tlaasik/vgafb/src/VgaFB_modes.cpp

/*

VgaFB_modes.cpp

Minimalistic VGA framebuffer hardware and software for microcontrollers
https://github.com/tlaasik/vgafb/

-------------------------------------------------------------------------------

Copyright (c) 2017, toomas.laasik@gmail.com
All rights reserved.

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
-------------------------------------------------------------------------------

Timing info used is taken from here:
http://martin.hinner.info/vga/timing.html

*/
#include "VgaFB_core.h"

// VESA 800x600@60Hz  hsync:37.9kHz pxclk:40.0MHz  800 840 968 1056  600 601 605 628  +hsync +vsync
vgamode_t vgamode_400x300_60Hz_20MHz = { 400, 420, 484, 526,  600, 601, 605, 628,  2, VGAFLAG_NONE };
vgamode_t vgamode_240x240_60Hz_20MHz = { 240, 344, 408, 526,  480, 601, 605, 628,  2, VGAFLAG_NONE };

// VESA 640x480@75Hz  hsync:37.5kHz pxclk:31.5MHz  640 656 720 840  480 481 484 500  -hsync -vsync
// modified hTotal because 840/16=52.5. pxclk is not exact, this mode should ideally use 31.5MHz
vgamode_t vgamode_640x480_75Hz_32MHz = { 640, 656, 720, 848,  480, 481, 484, 500,  1, (vgaflags_t)(VGAFLAG_INVERTED_VSYNC | VGAFLAG_INVERTED_HSYNC) };
vgamode_t vgamode_320x240_75Hz_16MHz = { 320, 328, 360, 424,  480, 481, 484, 500,  2, (vgaflags_t)(VGAFLAG_INVERTED_VSYNC | VGAFLAG_INVERTED_HSYNC) };

// VESA 640x400@85Hz  hsync:37.9kHz pxclk:31.5MHz  640 672 736 832  400 401 404 445 -hsync +vsync
vgamode_t vgamode_640x400_85Hz_32MHz = { 640, 672, 736, 832,  400, 401, 404, 445,  1, VGAFLAG_INVERTED_HSYNC };
vgamode_t vgamode_320x200_85Hz_16MHz = { 320, 336, 368, 416,  400, 401, 404, 445,  2, VGAFLAG_INVERTED_HSYNC };

// VESA 640x480@60Hz  hsync:31.5kHz pxclk:25.2MHz  640 656 752 800  480 490 492 525  -hsync -vsync
// pxclk is not exact, this mode should ideally use 25.175MHz
vgamode_t vgamode_640x480_60Hz_25MHz = { 640, 656, 752, 800,  480, 490, 492, 525,  1, (vgaflags_t)(VGAFLAG_INVERTED_VSYNC | VGAFLAG_INVERTED_HSYNC) };
vgamode_t vgamode_320x240_60Hz_12_6MHz = { 320, 328, 376, 400,  480, 490, 492, 525,  2, (vgaflags_t)(VGAFLAG_INVERTED_VSYNC | VGAFLAG_INVERTED_HSYNC) };
vgamode_t vgamode_160x120_60Hz_6_3MHz = { 160, 168, 192, 200,  480, 490, 492, 525,  4, (vgaflags_t)(VGAFLAG_INVERTED_VSYNC | VGAFLAG_INVERTED_HSYNC) };

// test
//vgamode_t vgamode_test = { 320, 336, 368, 416,  2, 4, 5, 6,  2, VGAFLAG_INVERTED_HSYNC };
